ShlokVaidya/HackBoard-v4.0/images/Screenshot 2026-02-05 151252.png

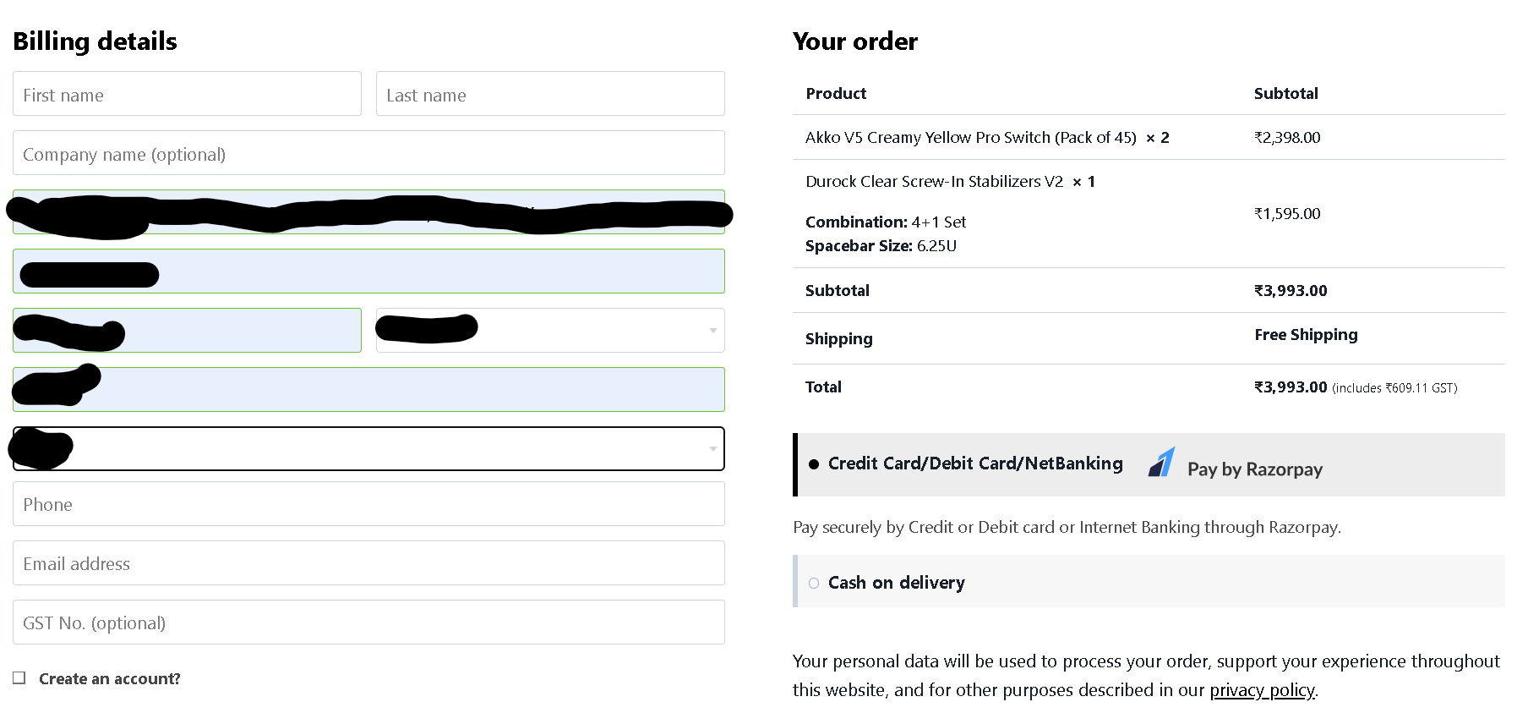
images/Screenshot 2026-02-05 151252.png
