ShlokVaidya/HackBoard-v4.0/images/Screenshot 2026-02-05 162554.png

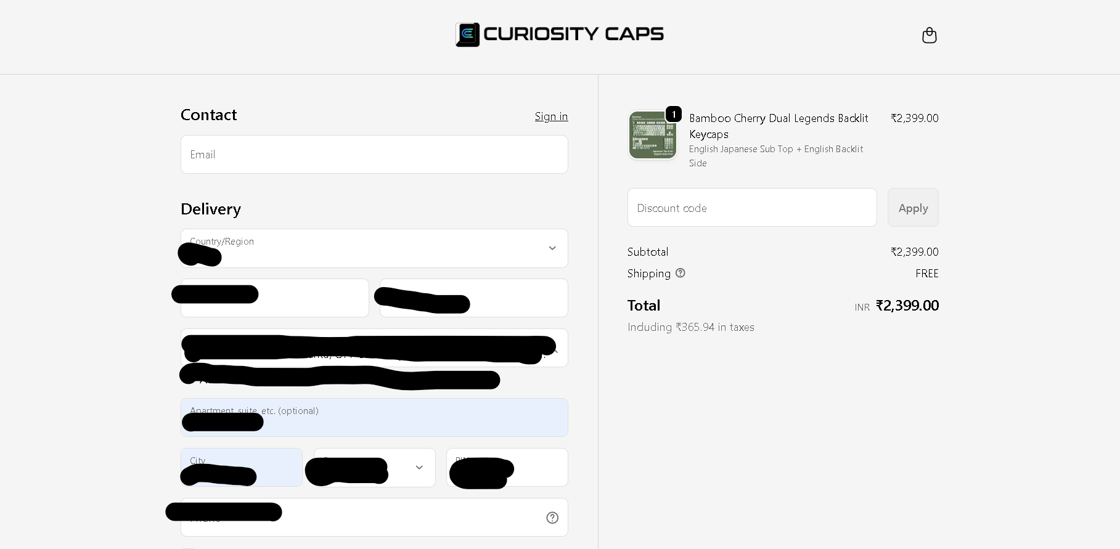
images/Screenshot 2026-02-05 162554.png
