ShlokVaidya/HackBoard-v4.0/images/Screenshot 2026-02-05 163637.png

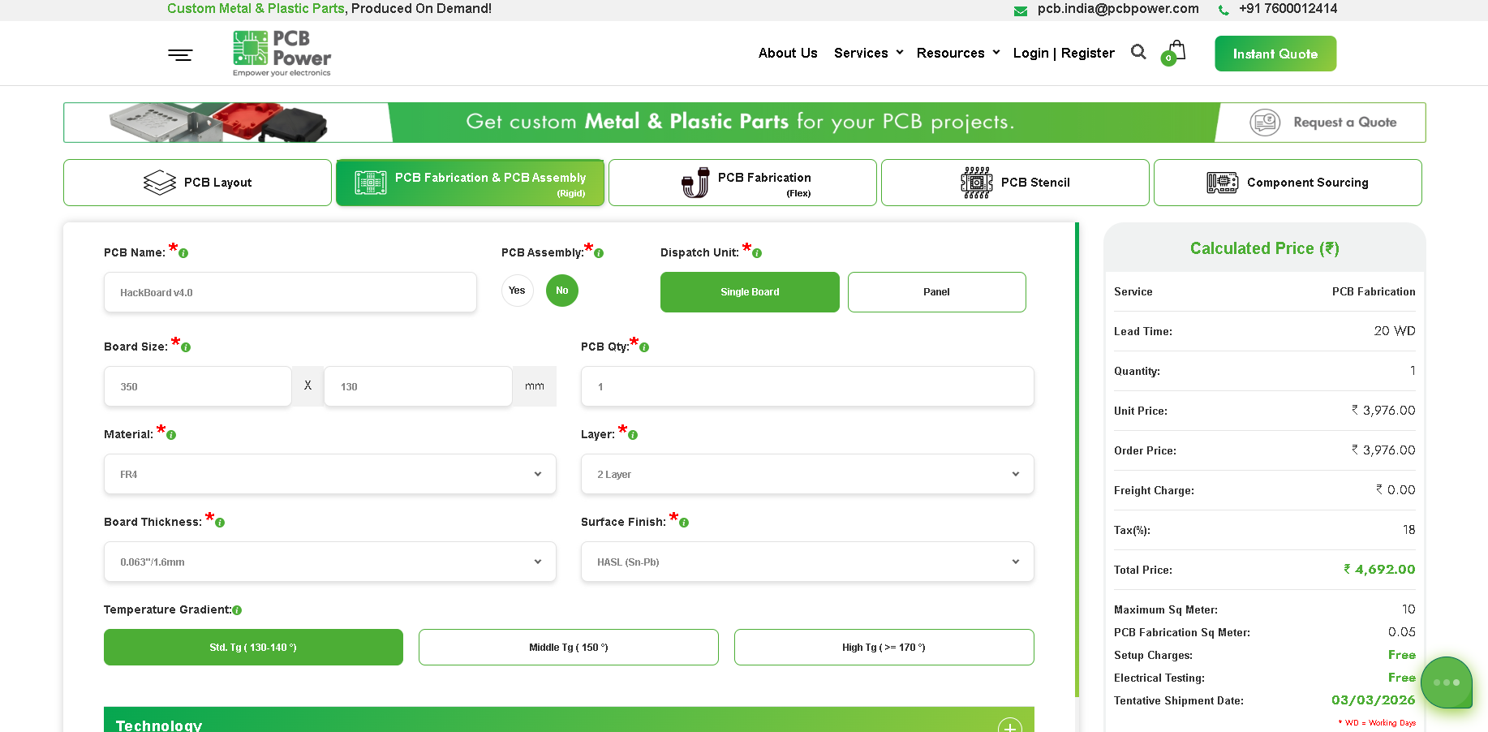
images/Screenshot 2026-02-05 163637.png
